NaboriRuta/2083-super-pit/swx-files/Microassemblies/Super Pit Bottom Half.SLDASM

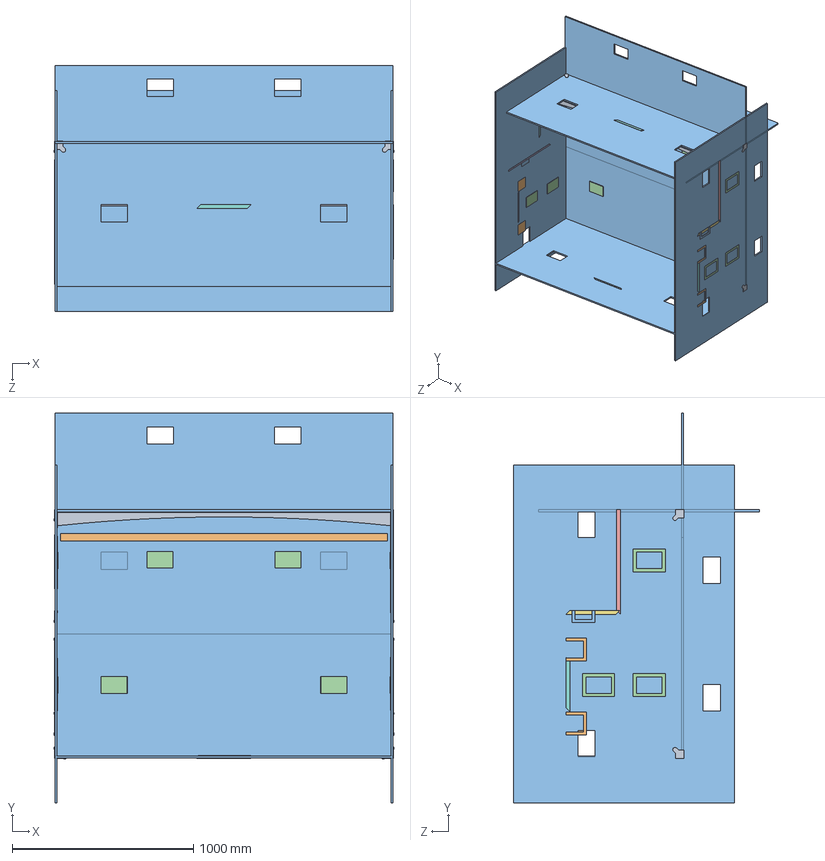
[picture p6: CAD file, 2025-05-05]
swx-files/Microassemblies/Super Pit Bottom Half.SLDASM
1872.8 x 2153.4 x 1358.9 mm
Plywood Panels x 6
Panel Joiner
Corner Bracket x 4
Tongue Extrusion x 4
Tongue Extrusion Alt 1 x 2
Tongue Extrusion Alt 2
Tongue Extrusion Alt 3
Handle Bracket x 10
Recessed Latch Bracket - Hook x 2
Recessed Latch Bracket - Twist x 4
Support Structure
