NaboriRuta/2083-super-pit/swx-files/Parts/Crank Handle Extension Thing Because Pit Crew Lost The Handle.SLDPRT

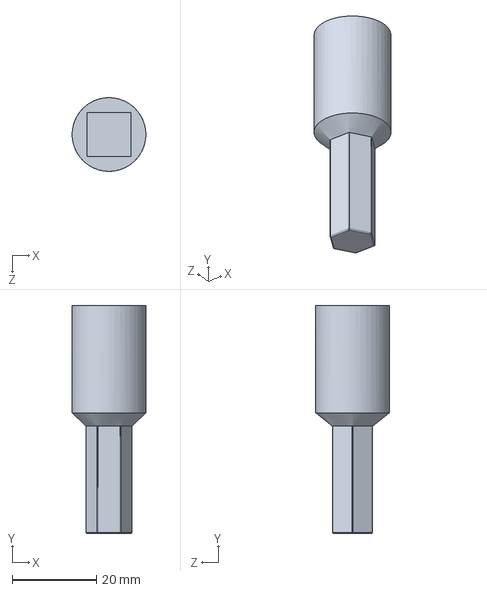
[picture p16: CAD file, 2025-04-16]
swx-files/Parts/Crank Handle Extension Thing Because Pit Crew Lost The Handle.SLDPRT
17.5 x 54.0 x 17.5 mm
