NaboriRuta/2083-super-pit/swx-files/Parts/Handles and Latches/Recessed Latch Bracket - Twist.SLDPRT

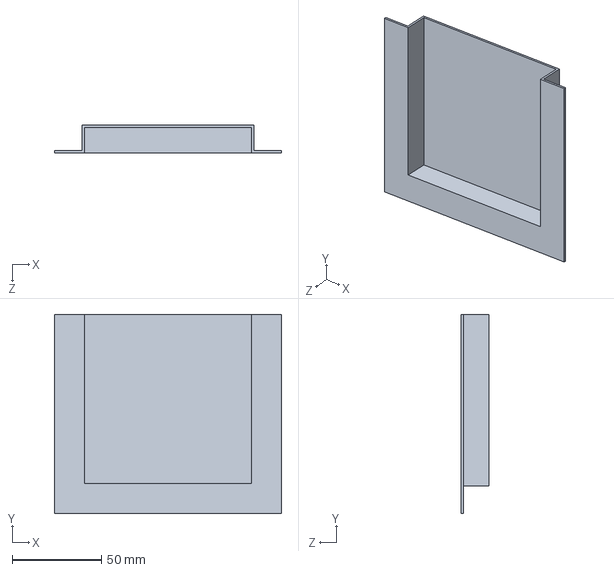
[picture p17: CAD file, 2025-02-28]
swx-files/Parts/Handles and Latches/Recessed Latch Bracket - Twist.SLDPRT
127.0 x 111.5 x 15.5 mm
