NaboriRuta/2083-super-pit/swx-files/Parts/Stand-Ins/Husky Toolbox Stand-in.SLDPRT

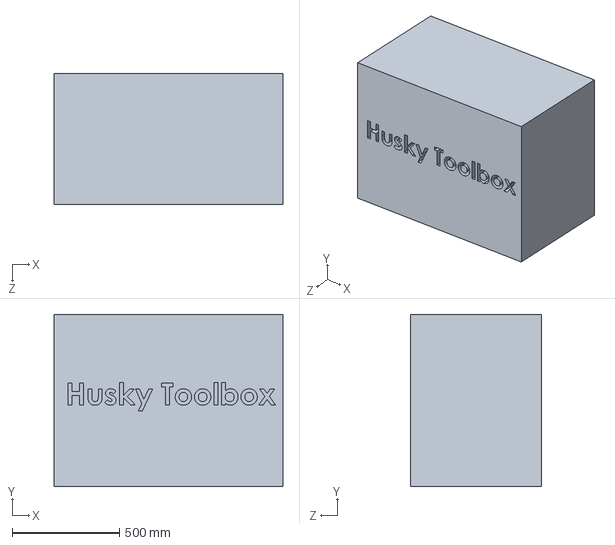
[picture p18: CAD file, 2025-04-03]
swx-files/Parts/Stand-Ins/Husky Toolbox Stand-in.SLDPRT
1066.8 x 803.3 x 609.6 mm
