NaboriRuta/2083-super-pit/step-files/Microassemblies/Cart Thing.STEP

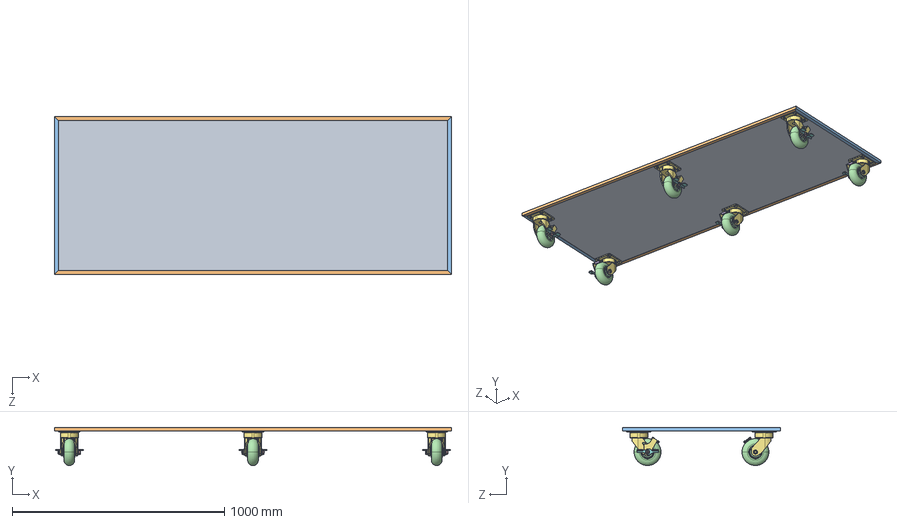
[picture p19: CAD file, 2025-04-03]
step-files/Microassemblies/Cart Thing.STEP
1870.2 x 179.4 x 743.1 mm
Plywood Panels_Cart Thing
U-shape Extrusion (Non-Corner Edges)_Horizontal Front Cover x 2
U-shape Extrusion (Non-Corner Edges)_Along Z Cart Thing x 2
2793N22_High-Capacity Easy-Turn Caster with Polyurethane Wheel_2793N22 x 6
