NaboriRuta/2083-super-pit/step-files/Parts/Plywood Divider.STEP

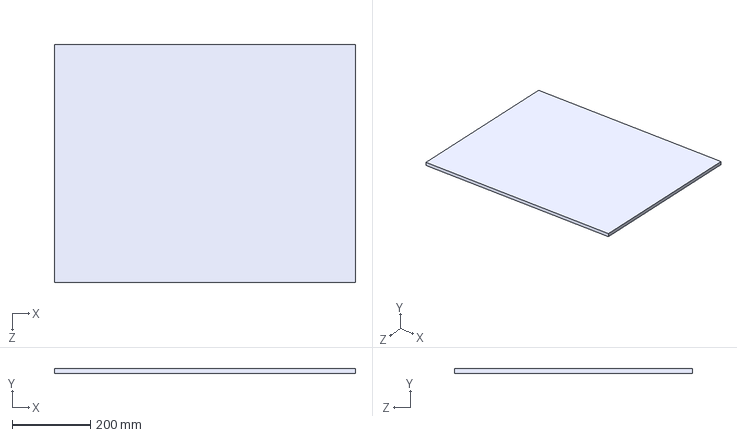
[picture p20: CAD file, 2025-04-03]
step-files/Parts/Plywood Divider.STEP
771.5 x 11.9 x 609.6 mm
