NaboriRuta/2083-super-pit/step-files/Parts/Stand-Ins/Butcher Block Stand-In.STEP

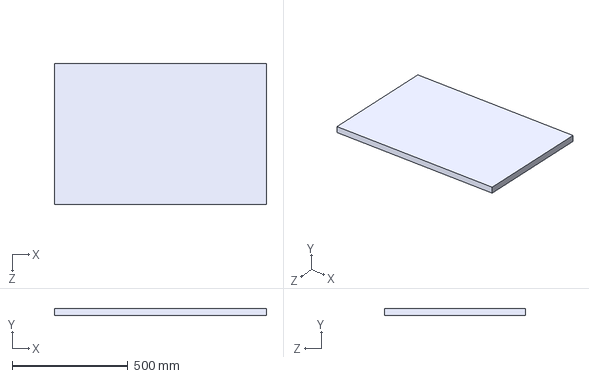
[picture p21: CAD file, 2025-04-03]
step-files/Parts/Stand-Ins/Butcher Block Stand-In.STEP
914.4 x 31.8 x 609.6 mm
