NaboriRuta/2083-super-pit/swx-files/Parts/Edges and Corners/Tongue Extrusion Alt 2.SLDPRT

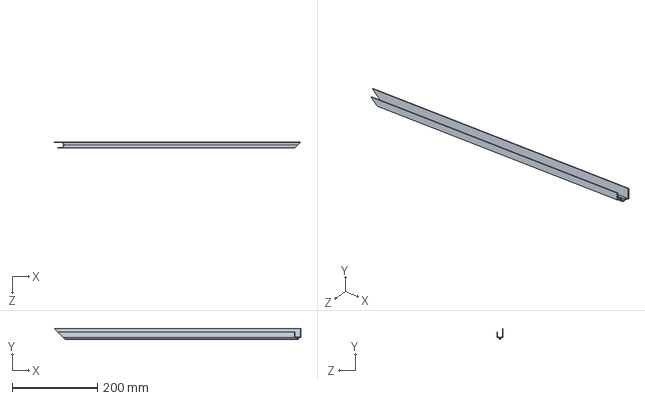
[picture p22: CAD file, 2025-02-10]
swx-files/Parts/Edges and Corners/Tongue Extrusion Alt 2.SLDPRT
579.4 x 26.2 x 15.2 mm
