NaboriRuta/2083-super-pit/swx-files/Parts/Handles and Latches/Handle Bracket.SLDPRT

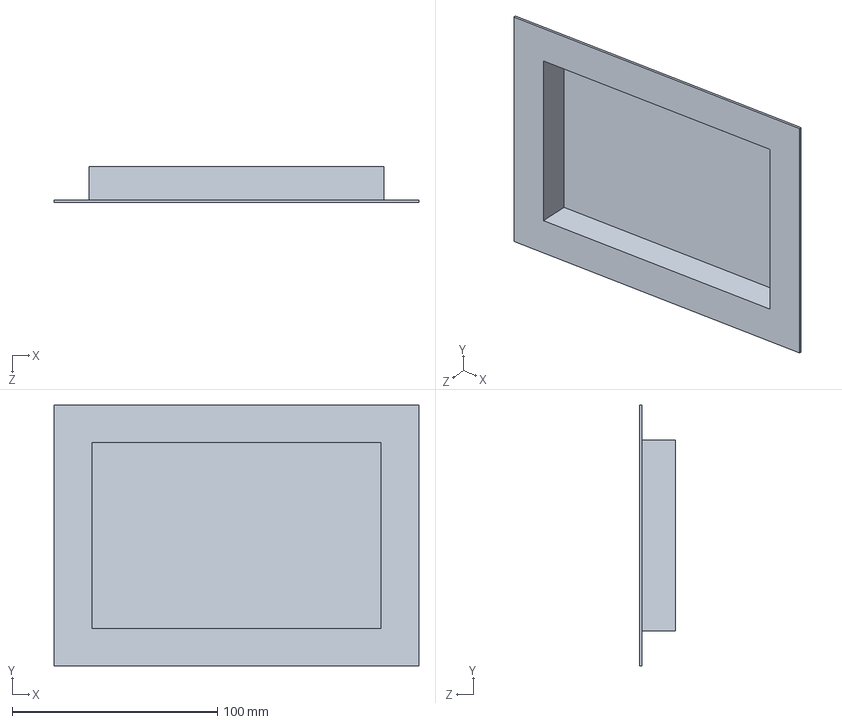
[picture p23: CAD file, 2025-02-28]
swx-files/Parts/Handles and Latches/Handle Bracket.SLDPRT
177.8 x 127.0 x 17.8 mm
