NaboriRuta/2083-super-pit/swx-files/Parts/Stand-Ins/Top of Red Toolbox Stand-In.SLDPRT

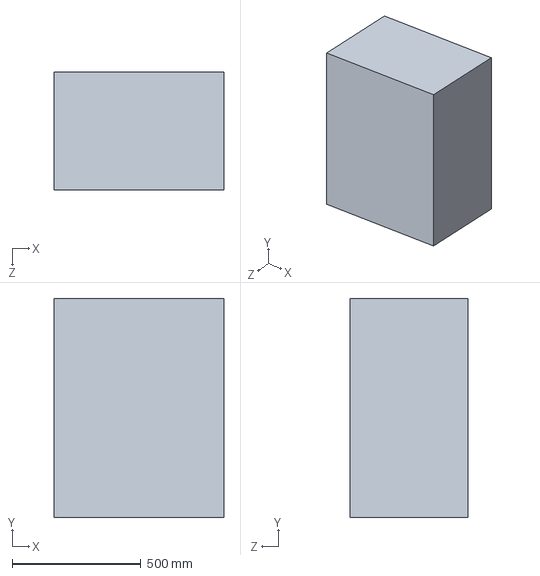
[picture p24: CAD file, 2025-04-03]
swx-files/Parts/Stand-Ins/Top of Red Toolbox Stand-In.SLDPRT
660.4 x 850.9 x 457.2 mm
