NaboriRuta/2083-super-pit/step-files/Microassemblies/Super Pit Front Cover.STEP

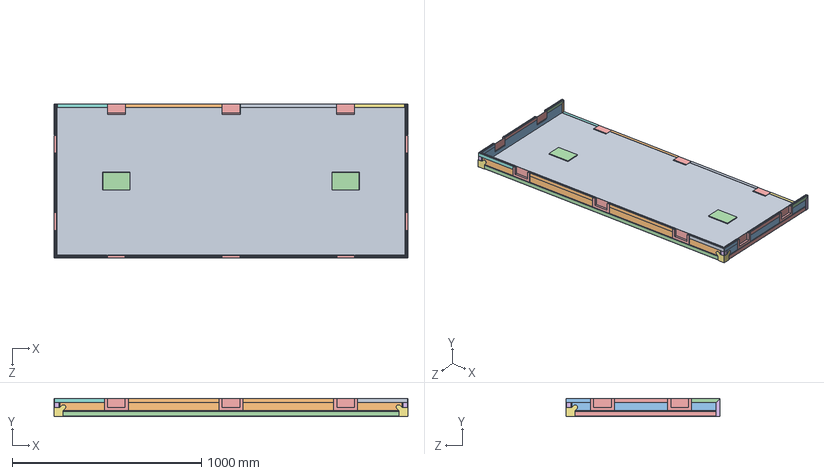
[picture p25: CAD file, 2025-04-03]
step-files/Microassemblies/Super Pit Front Cover.STEP
1872.8 x 96.6 x 816.6 mm
Plywood Panels_Front Cover Main Piece
Plywood Panels_Front Cover Long Sides
Plywood Panels_Front Cover Short Sides x 2
Single Angle Extrusion (Edges)_Along X
Single Angle Extrusion (Edges)_Along Y Front Cover x 2
Single Angle Extrusion (Edges)_Along Z Front Cover x 2
Corner Bracket x 2
Groove Extrusion_Horizontal x 2
Groove Extrusion Alt 1_Along Z Right Front Cover
Groove Extrusion_Right Vertical Front Cover
Groove Extrusion Alt 1_Left Vertical Front Cover
Groove Extrusion_Along Z Left Front Cover
Handle Bracket x 2
Recessed Latch Bracket - Hook x 10
