NaboriRuta/2083-super-pit/swx-files/Parts/10x10 square.SLDPRT

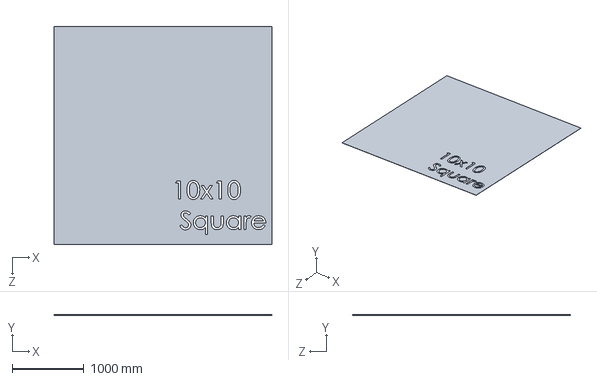
[picture p26: CAD file, 2025-02-10]
swx-files/Parts/10x10 square.SLDPRT
3048.0 x 2.54 x 3048.0 mm
