NaboriRuta/2083-super-pit/swx-files/Parts/Stand-Ins/Battery Stand-In.SLDPRT

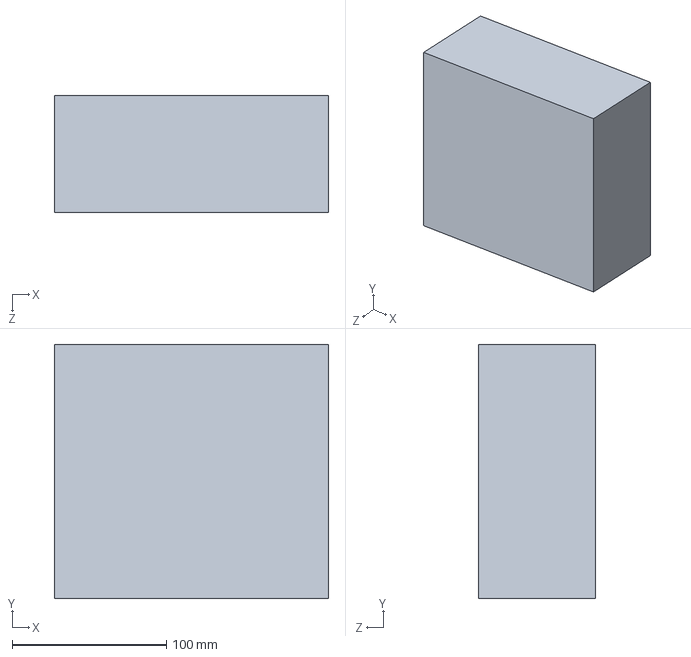
[picture p27: CAD file, 2025-02-10]
swx-files/Parts/Stand-Ins/Battery Stand-In.SLDPRT
177.8 x 165.1 x 76.2 mm
