NaboriRuta/2083-super-pit/swx-files/Parts/Edges and Corners/Groove Extrusion Alt 1.SLDPRT

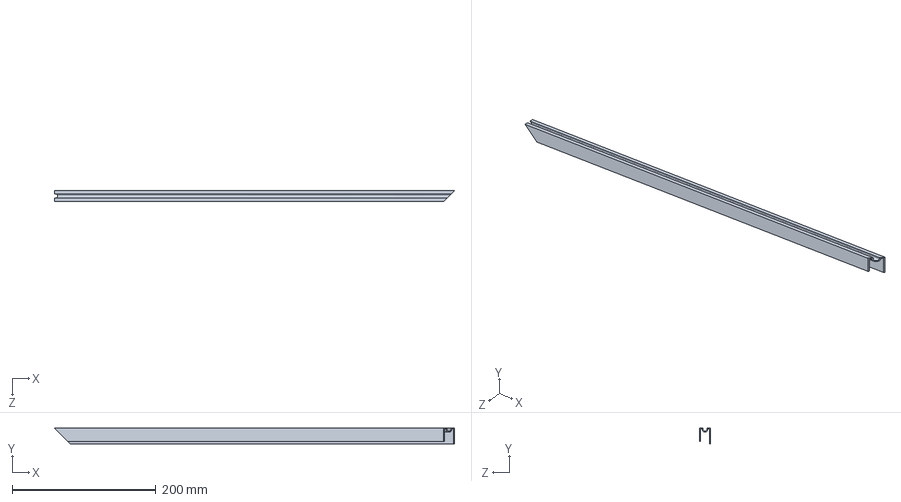
[picture p28: CAD file, 2025-02-10]
swx-files/Parts/Edges and Corners/Groove Extrusion Alt 1.SLDPRT
557.2 x 21.8 x 15.2 mm
