NaboriRuta/2083-super-pit/swx-files/Parts/Plywood Panels.SLDPRT

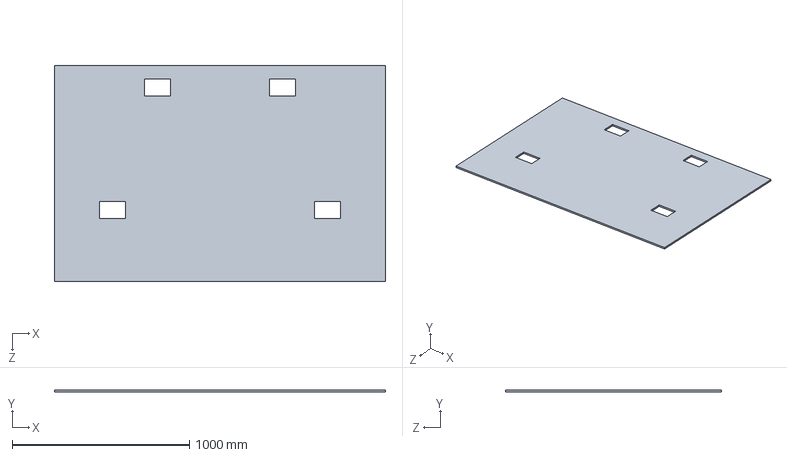
[picture p29: CAD file, 2025-02-10]
swx-files/Parts/Plywood Panels.SLDPRT
1866.9 x 11.9 x 1219.2 mm
