NaboriRuta/2083-super-pit/swx-files/Parts/Edges and Corners/Tongue Extrusion.SLDPRT

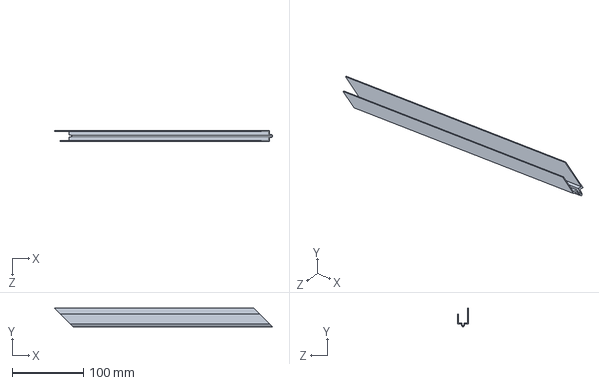
[picture p30: CAD file, 2025-02-10]
swx-files/Parts/Edges and Corners/Tongue Extrusion.SLDPRT
305.6 x 26.2 x 15.2 mm
