NaboriRuta/2083-super-pit/swx-files/Parts/Stand-Ins/Cart With Bot Stand-In.SLDPRT

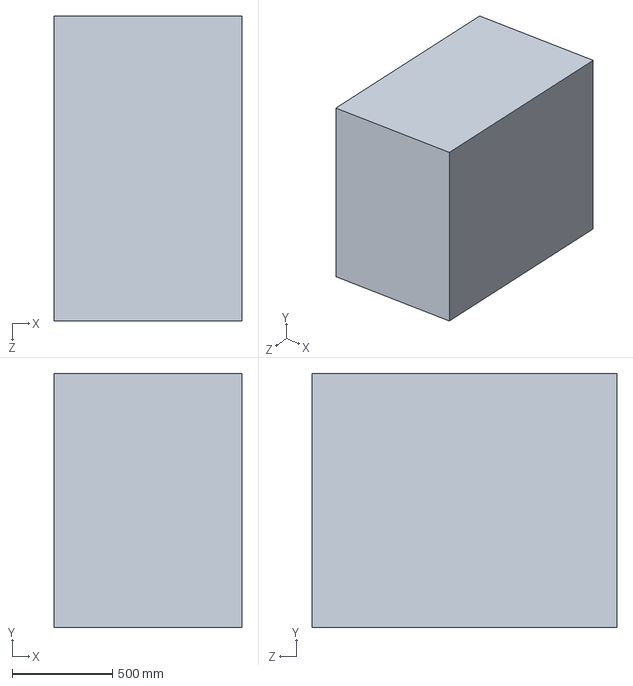
[picture p31: CAD file, 2025-02-10]
swx-files/Parts/Stand-Ins/Cart With Bot Stand-In.SLDPRT
939.8 x 1270.0 x 1524.0 mm
