NaboriRuta/2083-super-pit/swx-files/Parts/Edges and Corners/Tongue Extrusion Alt 1.SLDPRT

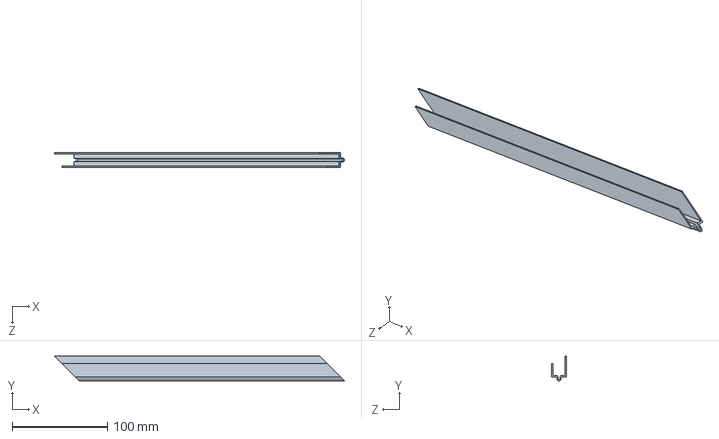
[picture p32: CAD file, 2025-02-10]
swx-files/Parts/Edges and Corners/Tongue Extrusion Alt 1.SLDPRT
304.8 x 26.2 x 15.2 mm
