NaboriRuta/2083-super-pit/swx-files/Parts/Edges and Corners/U-shape Extrusion (Non-Corner Edges).SLDPRT

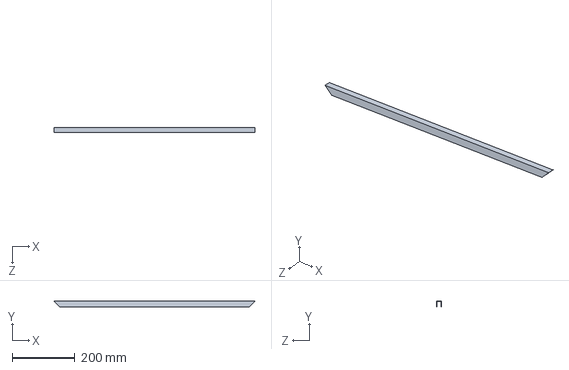
[picture p33: CAD file, 2025-02-10]
swx-files/Parts/Edges and Corners/U-shape Extrusion (Non-Corner Edges).SLDPRT
641.3 x 19.1 x 16.0 mm
