NaboriRuta/2083-super-pit/swx-files/Parts/Edges and Corners/Corner Bracket.SLDPRT

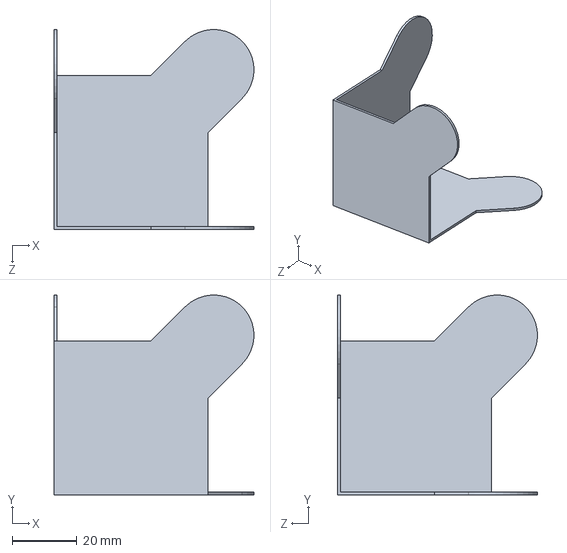
[picture p34: CAD file, 2025-02-10]
swx-files/Parts/Edges and Corners/Corner Bracket.SLDPRT
62.0 x 62.0 x 62.0 mm
