NaboriRuta/2083-super-pit/swx-files/Microassemblies/Cart Thing.SLDASM

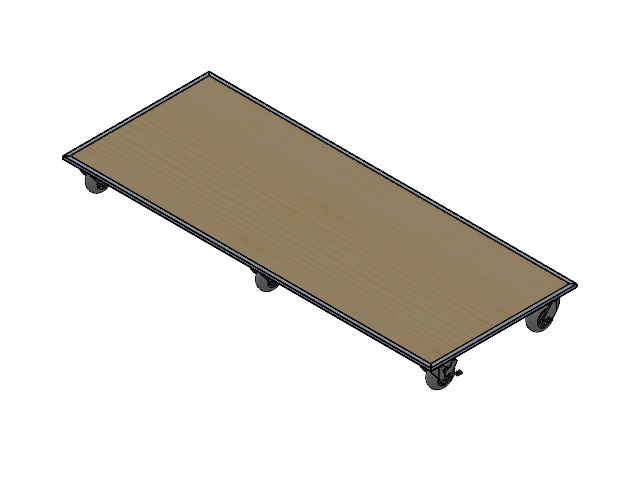
[picture p35: CAD file, 2025-05-05]
swx-files/Microassemblies/Cart Thing.SLDASM
Plywood Panels
U-shape Extrusion (Non-Corner Edges) x 4
2793N22_High-Capacity Easy-Turn Caster with Polyurethane Wheel x 6
